SenudaHR/Five-Band-Audio-Equalizer/simulations/full.asc

C1: cap; 220n
C2: cap; 470n
C3: cap; 220n
C4: cap; 220n
C5: cap; 100n
C6: cap; 100n
C7: cap; 10n
C8: cap; 10n
C9: cap; 33n
C10: cap; 33n
C11: cap; 10n
C12: cap; 10n
C13: cap; 15n
C14: cap; 15n
C15: cap; 6.8n
C16: cap; 6.8n
C17: cap; 10n
C18: cap; 10n
C19: cap; 6.8n
C20: cap; 6.8n
C21: cap; 100n
C22: polcap; 4.7µ
C23: polcap; 1µ
C24: polcap; 10µ
R1: res; 2.2k
R2: res; 1.2k
R3: res; 47k
R4: res; 27k
R5: res; 3.9k
R6: res; 15k
R7: res; 3.3k
R8: res; 15k
R9: res; 47k
R10: res; 10k
R11: res; 6.8k
R12: res; 6.8k
R13: res; 2.7k
R14: res; 3.3k
R15: res; 10k
R16: res; 8.2k
R17: res; 1k
R18: res; 1k
R19: res; 2.2k
R20: res; 2.7k
R21: res; 8.2k
R22: res; 6.8k
R23: res; 390
R24: res; 330
R25: res; 2.2k
R26: res; 1.8k
R27: res; 5.6k
R28: res; 5.6k
R29: res; 100k
R30: res; 100k
R31: res; 2.2k
R32: res; 30k
R36: res; 1k
R37: res; 1k
R38: res; 1k
R39: res; 1k
R40: res; 1k
R41: res; 1k
R42: res; 1k
R43: res; 1k
R44: res; 1k
R45: res; 1k
R46: res; 1k
R47: res; 1k
R48: res; 1k
R49: res; 1k
R50: res; 1k
R51: res; 1k
U1: TL072
U2: TL072
U3: TL072
U4: TL072
U5: TL072
U6: TL072
U7: TL072
U8: TL072
U9: TL072
U10: TL072
U11: TL072
U14: TL072
U15: TL072
U16: TL072
U17: TL072
U18: TL072
U19: TL072
U20: TL072
V1: voltage; SINE(0 160m 1k); AC 100m
V3: voltage; 12
V4: voltage; 12
Named nets: 0, V+, V-, Vout
.ac dec 100 10 100k
20-300 Hz BPF
300 Hz- 1 kHz
1 kHz- 4 kHz
4 kHz- 10 kHz
10 kHz - 20 kHz
Adder/ Gain Controller
Output Buffer
