SenudaHR/Five-Band-Audio-Equalizer/simulations/pre amp.asc

C1: cap; 100n
C4: polcap; 4.7µ
C5: polcap; 1µ
C6: polcap; 10µ
R1: res; 100k
R2: res; 100k
R3: res; 2.2k
R4: res; 30k
R5: res; 100k
U1: TL072
V1: voltage; SINE(0 160m 1k)
V2: voltage; 12
Named nets: 0, Vo
.tran 30m
